Dominik-Workshop/Electronic_load/datasheets/ATmega328p_pinout.png

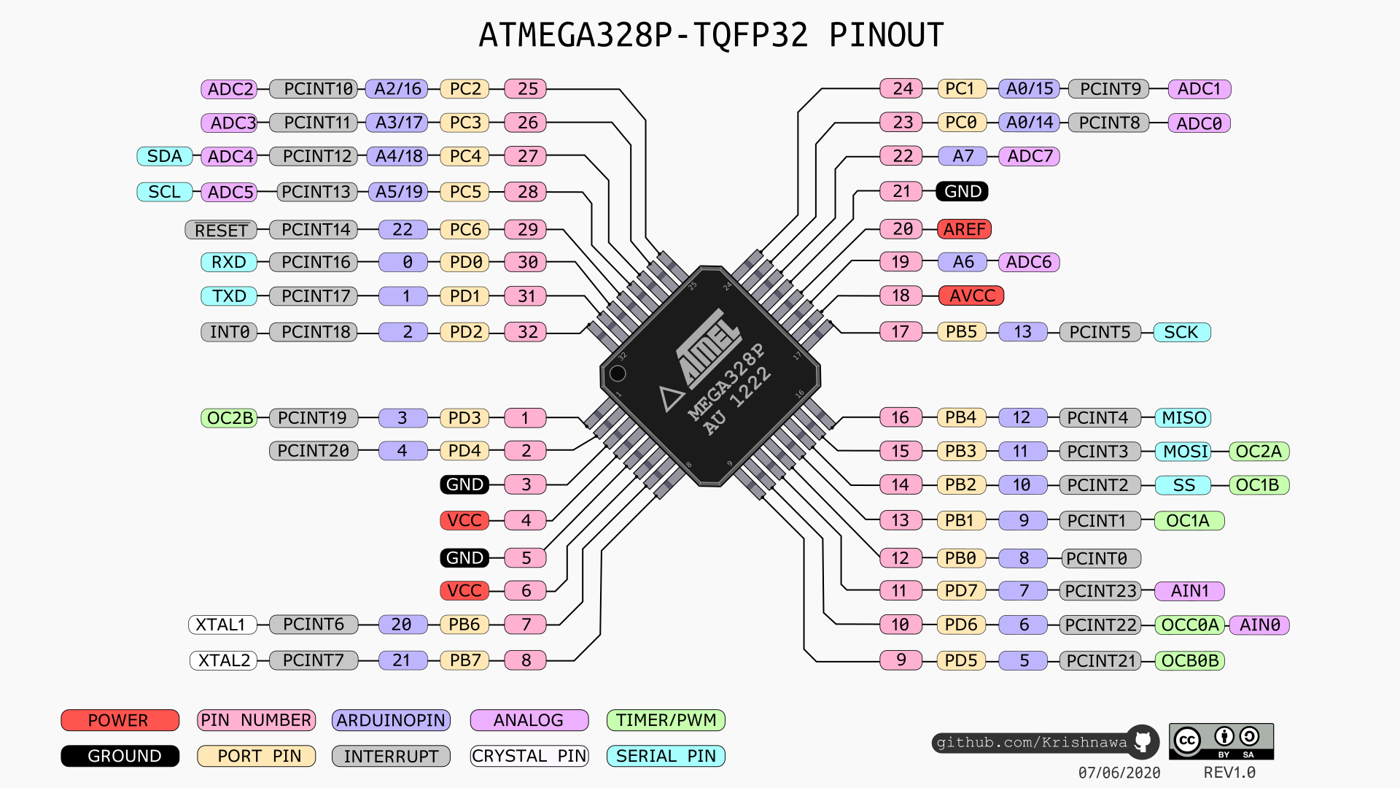
datasheets/ATmega328p_pinout.png
