Dominik-Workshop/Electronic_load/desktop_app/dox/html/class_electronic__load__app__coll__graph.png

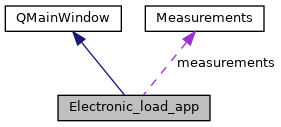
desktop_app/dox/html/class_electronic__load__app__coll__graph.png
