Dominik-Workshop/Electronic_load/desktop_app/dox/html/dir_4aa64b0872d36146e049722e293482e3_dep.png

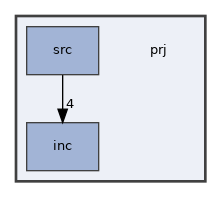
desktop_app/dox/html/dir_4aa64b0872d36146e049722e293482e3_dep.png
