Dominik-Workshop/Electronic_load/desktop_app/dox/html/dir_400757c3a0df52e783ed9699284f29ce_dep.png

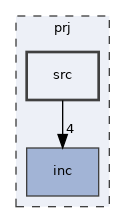
desktop_app/dox/html/dir_400757c3a0df52e783ed9699284f29ce_dep.png
