Dominik-Workshop/Electronic_load/desktop_app/dox/html/dir_72345776cd6700fb0dedb8f1faaa0c00_dep.png

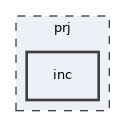
desktop_app/dox/html/dir_72345776cd6700fb0dedb8f1faaa0c00_dep.png
