Dominik-Workshop/Electronic_load/desktop_app/dox/html/electronic__load__app_8cpp__incl.png

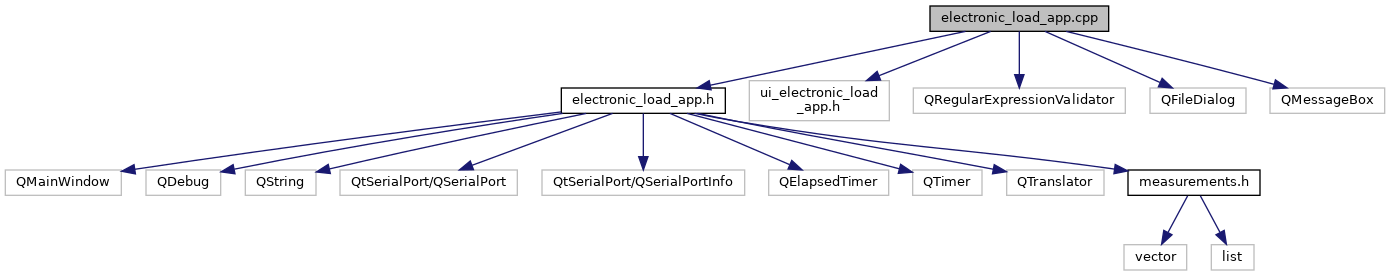
desktop_app/dox/html/electronic__load__app_8cpp__incl.png
