Dominik-Workshop/Electronic_load/images/pictures/front.jpg

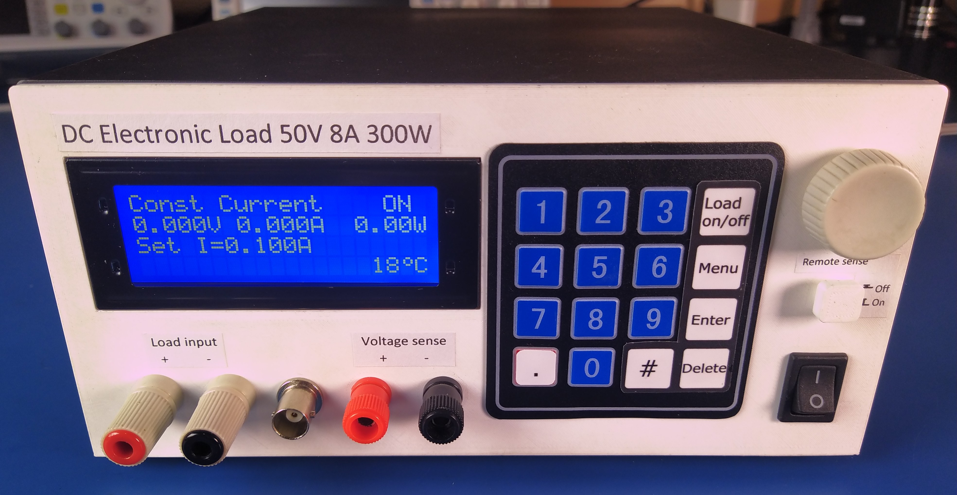
images/pictures/front.jpg
