Dominik-Workshop/Electronic_load/images/pictures/insides2.jpg

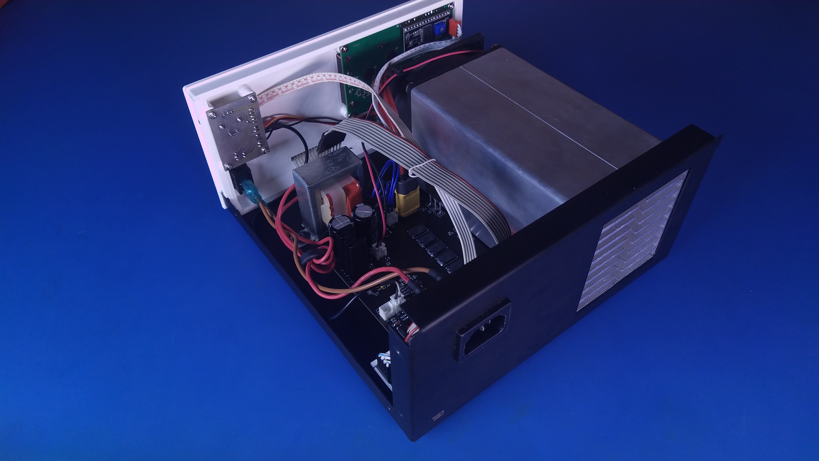
images/pictures/insides2.jpg
