Dominik-Workshop/Electronic_load/images/pictures/insides.jpg

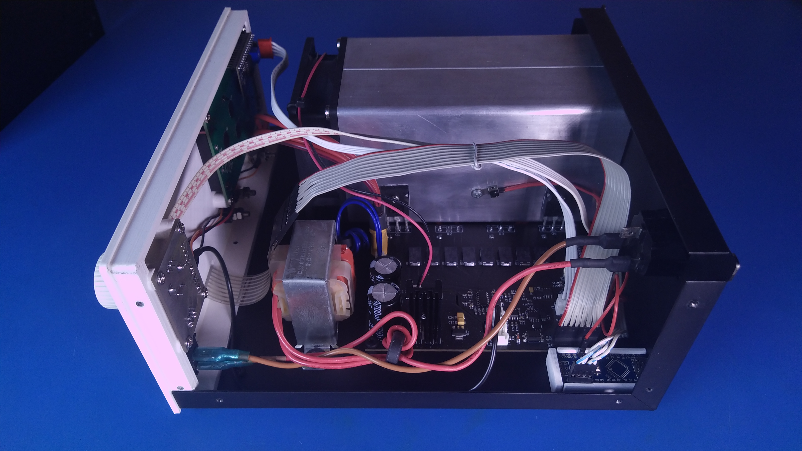
images/pictures/insides.jpg
