Dominik-Workshop/Electronic_load/images/pictures/main_PCB-no-background.png

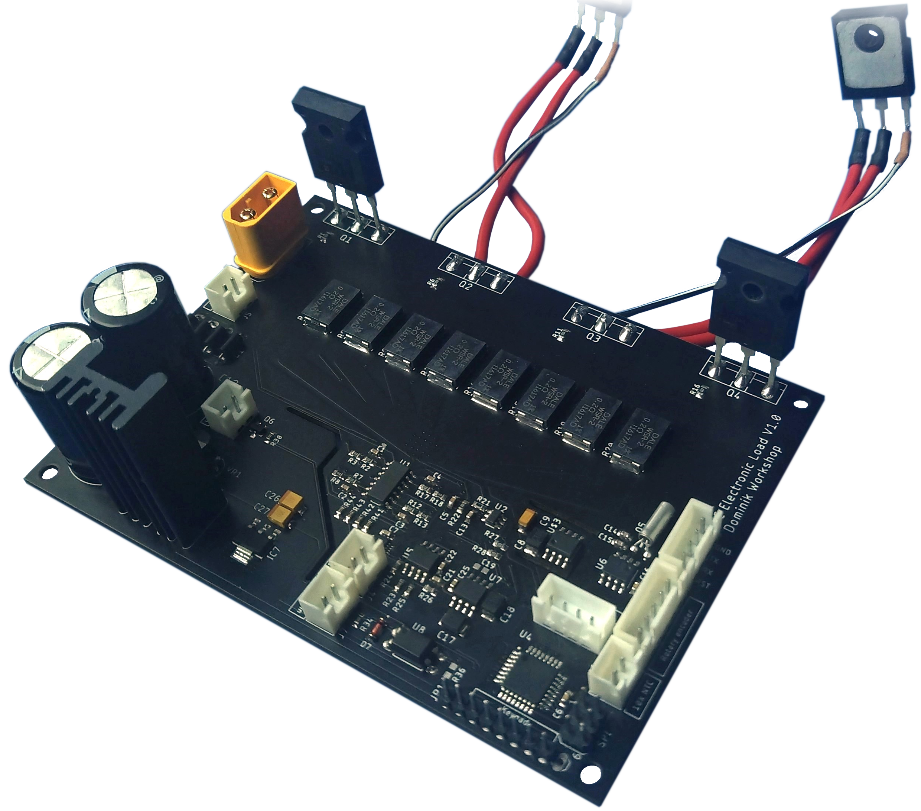
images/pictures/main_PCB-no-background.png
