Dominik-Workshop/Electronic_load/images/pictures/main_PCB.jpg

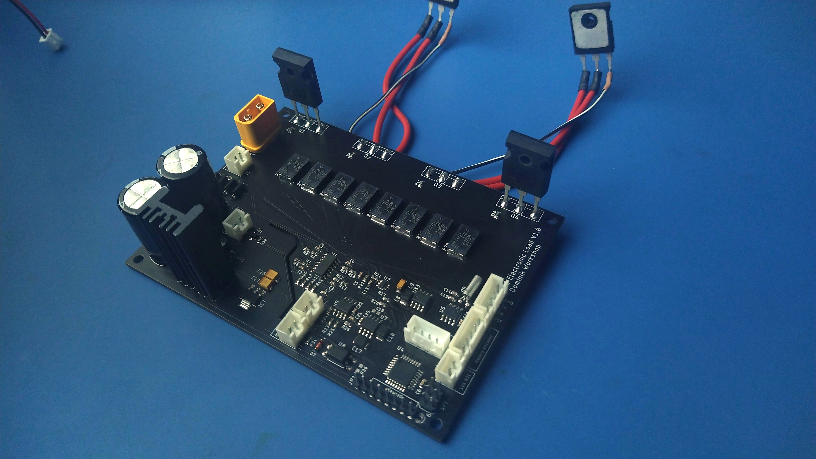
images/pictures/main_PCB.jpg
