Dominik-Workshop/Electronic_load/images/pictures/rear.jpg

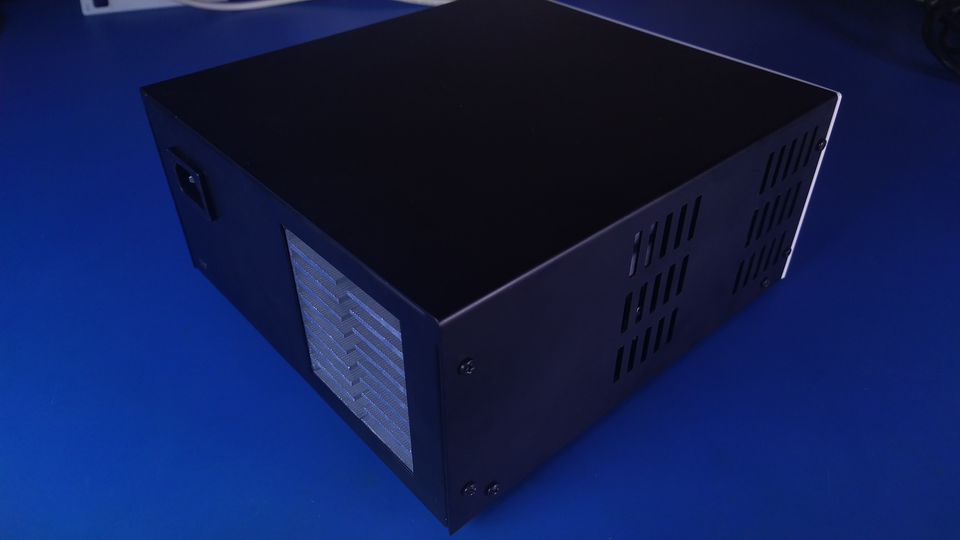
images/pictures/rear.jpg
