Dominik-Workshop/Electronic_load/images/renders/front_cover.PNG

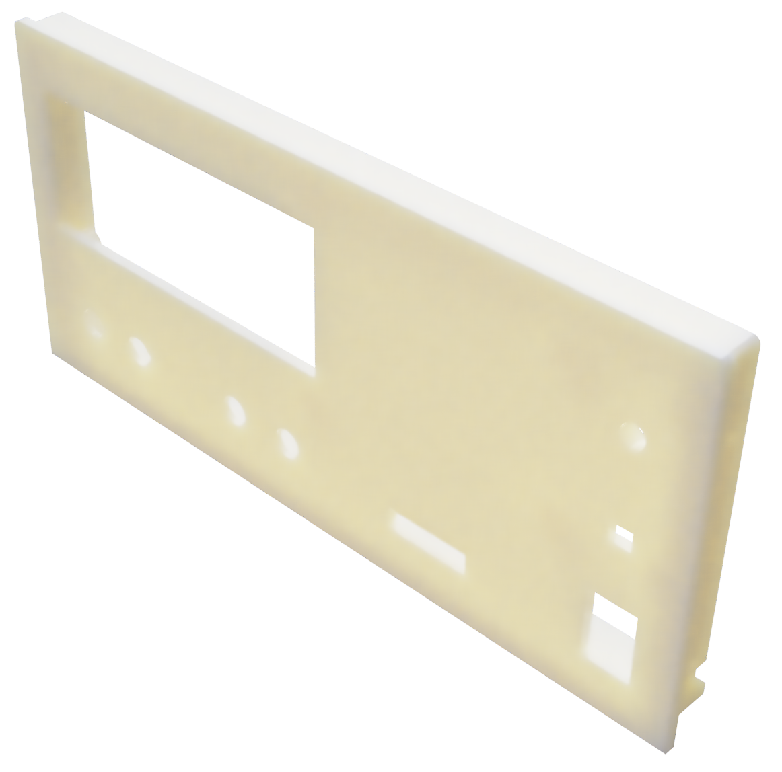
images/renders/front_cover.PNG
