Dominik-Workshop/Electronic_load/images/renders/metal_case_bottom.png

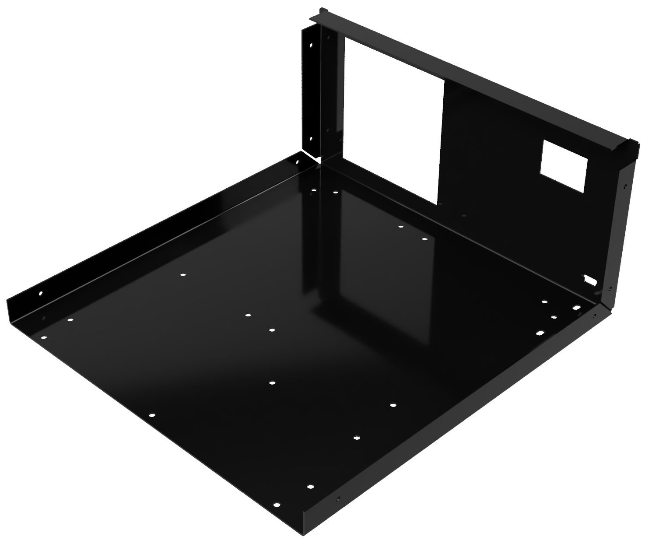
images/renders/metal_case_bottom.png
