Dominik-Workshop/Electronic_load/images/renders/metal_case_bottom_feet.png

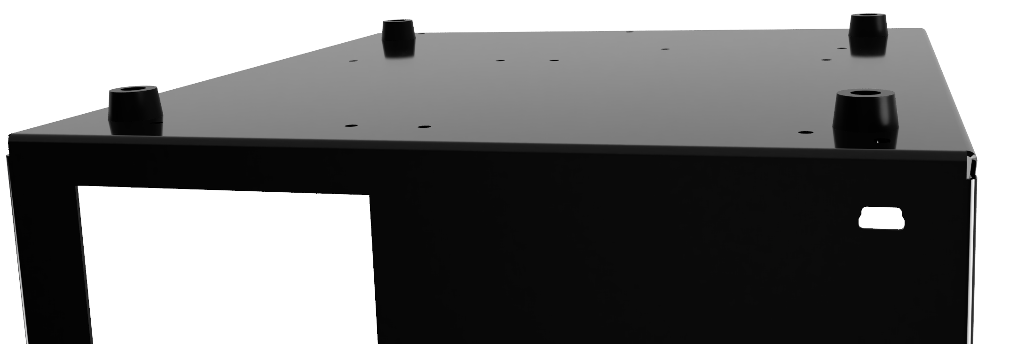
images/renders/metal_case_bottom_feet.png
