Dominik-Workshop/Electronic_load/images/renders/metal_case_top.png

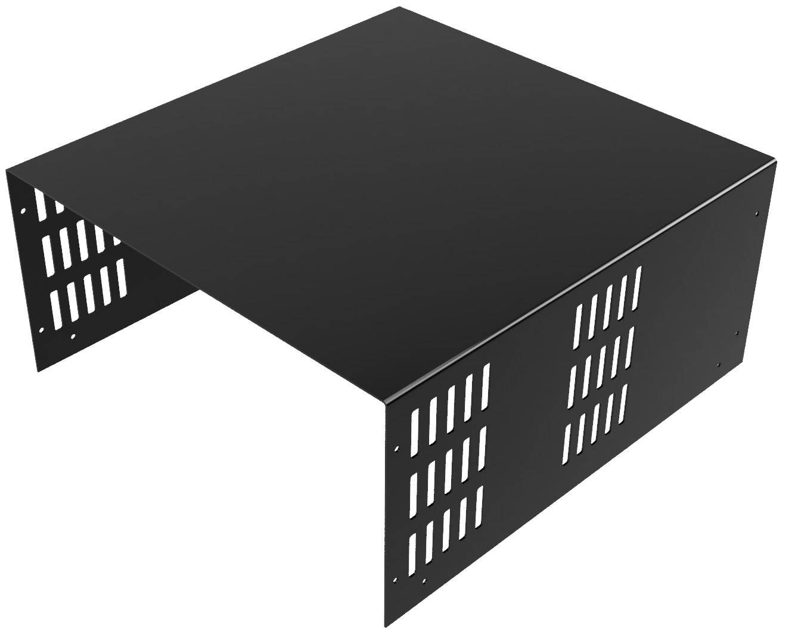
images/renders/metal_case_top.png
