Dominik-Workshop/Electronic_load/keypad_sticker_final.png

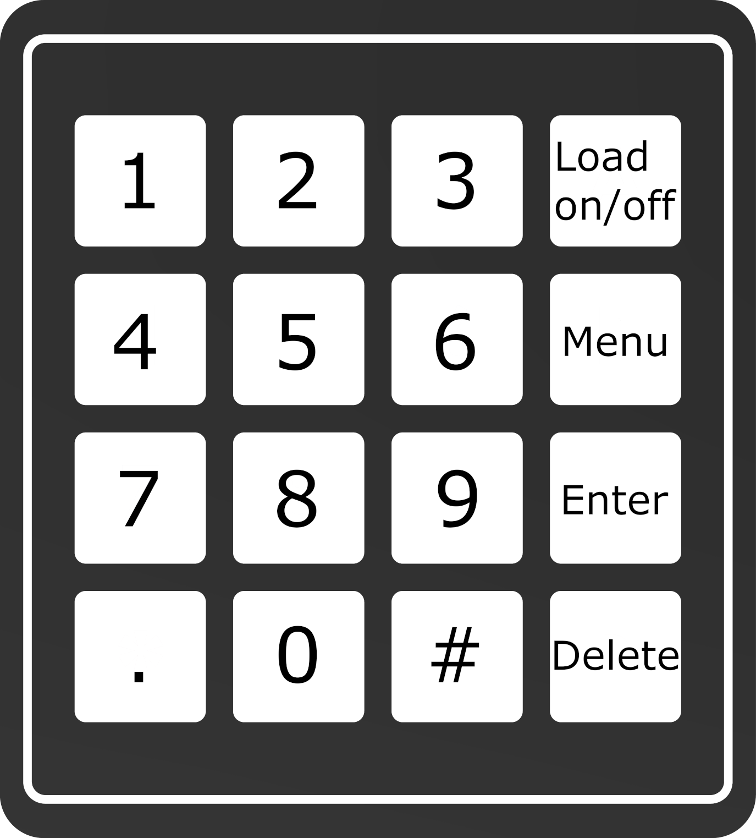
keypad_sticker_final.png
