Dominik-Workshop/Electronic_load/desktop_app/dox/html/measurements_8cpp__incl.png

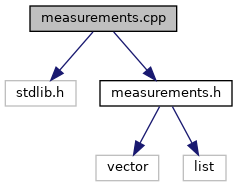
desktop_app/dox/html/measurements_8cpp__incl.png
