Dominik-Workshop/Electronic_load/desktop_app/dox/html/measurements_8h__dep__incl.png

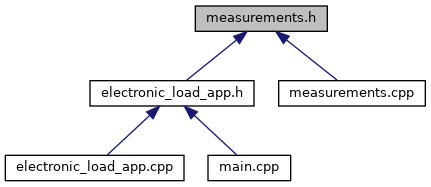
desktop_app/dox/html/measurements_8h__dep__incl.png
